prime6809/DragonMMC/DragonFirmware/rsdos/rsdos_mmc.asm

__rsdos
                use     coco-defs.asm
                
dhitok         equ     $e1                      ; highest 1.1 disk token                                     
cyear          equ     '2'                                      


;wd27           equ     $08                     ; uncomment this if using wd2797 on dragon/rs contoler
;wd27            equ     $00                     ; uncomment this if using standard rs-dos or wd2793

;WDRestore       equ     WDCmdRestore+StepRate30ms
;WDSeek          equ     WDCmdSeek+WDFlagVerify+StepRate30ms
;WDStepIn        equ     WDCmdStepIn+WDFlagUpdate+StepRate30ms
;WDStepOut       equ     WDCmdStepOut+WDFlagUpdate+StepRate30ms
;WDReadSector    equ     WDCmdReadSec+wd27       ; read sector command
;WDWriteSector   equ     WDCmdWriteSec+wd27      ; write sector command
;WDWriteTrack    equ     WDCmdWriteTrack

;
;
;
; file allocation table format
;
;
; the file allocation table (fat) contains the status of the granules on a diskette.
; the fat contains 6 control bytes followed by 68 data bytes (one per granule). only the
; first two of the six control bytes are used. a value of $ff is saved in unallocated
; granules. if bits 6 & 7 of the data byte are set, the granule is the last granule
; in a file and bits 0-5 are the number of used sectors in that granule. if bits 6 & 7
; are not set, the data byte contains the number of the next granule in the file.

; offsets to fat control bytes
fat0           equ     0                        ; active file counter : disk to ram fat image disable                                                              
fat1           equ     1                        ; valid data flag: 0=disk data valid, <> 0 = new fat                                                             
;                                         data - disk data invalid
;                2 to 5                   not used
fatcon         equ     6                        ; offset to start of fat data (68 bytes)                                                   
;
;;
;;;; directory entry format
;;
;
; the directory is used to keep track of how many files are stored on a diskette
; and where the file is stored on the disk. the first granule used by the file will
; allow the fat to track down all of the granules used by the file. if the first
; byte of the directory entry is zero, the file has been killed;
; if the first byte is $ff then the directory entry has never been used.
;
;                byte                                description

dirnam         equ     0                        ; file name                      
dirext         equ     8                        ; file extension                           
dirtyp         equ     11                       ; file type                       
dirasc         equ     12                       ; ascii flag                        
dirgrn         equ     13                       ; first granule in file                                   
dirlst         equ     14                       ; number of bytes in last sector                                            
;                16 to 31                            unused
;
;;
;;;; file control block format
;;
;
; the file structure of color trs dos is controlled by a file control block (fcb)
; the fcb contains 25 control bytes and a sector long (256 bytes) data buffer.
; the control bytes control the orderly flow of data from the computer's ram to
; the diskette and vice versa. the open command initializes the fcb; the input,
; output, write, print, get and put commands transfer data through the fcb and
; the close command turns off the fcb.

; tables of offsets to fcb control bytes

;;;;; random file
;                byte                                description
fcbtyp         equ     0                        ; file type: $40=random/direct, 0=closed                                                   
fcbdrv         equ     1                        ; drive number                         
fcbfgr         equ     2                        ; first granule in file                                  
fcbcgr         equ     3                        ; current granule being used                                       
fcbsec         equ     4                        ; current sector being used (1-9)                                            
;                5                                   unused
fcbpos         equ     6                        ; current print position - always zero in random files                                                                 
fcbrec         equ     7                        ; current record number                                  
fcbrln         equ     9                        ; random file record length                                      
fcbbuf         equ     11                       ; pointer to start of this file's random access buffer                                                                  
fcbsof         equ     13                       ; sector offset to current position in record                                                         
fcbflg         equ     15                       ; get/put flag: 0=put, 1=put                                        
;                16,17                               not used
fcbdir         equ     18                       ; directory entry number (0-71)                                           
fcblst         equ     19                       ; number of bytes in last sector of file                                                    

fcbget         equ     21                       ; 'get' record counter: how many characters have been                                                                 
;                                                    pulled out of the current record
fcbput         equ     23                       ; 'put' record counter: pointer to where in the record the next                                                                           
;                                                    byte will be 'put'
;fcbcon         equ     25                          ; offset to start of fcb data buffer (256 bytes)                                                            

;;;;; sequential file (some of these are commented out as they are defined above)
;                byte                                description
;fcbtyp         equ     0                           ; file type: $10=input, $20=output, 0=closed                                                       
;fcbdrv         equ     1                           ; drive number                         
;fcbfgr         equ     2                           ; first granule in file                                  
;fcbcgr         equ     3                           ; current granule being used                                       
;fcbsec         equ     4                           ; current sector being used (1-9)                                            
fcbcpt         equ     5                        ; input file: character pointer - points to next character in                                                                        
;                                                    file to be processed.
;                                                    output file: full sector flag - if it is 1 when the file is
;                                                    closed it means 256 bytes of the last sector have been used.
;fcbpos         equ     6                           ; current print position                                   
;fcbrec         equ     7                           ; current record number: how many whole sectors have been                                                                    
;                                                    input or output to a file.
;                9 to 15                             unused
fcbcfl         equ     16                       ; cache flag: 00=cache empty, $ff=cache full                                                        
fcbcdt         equ     17                       ; cache data byte                             
;fcbdir         equ     18                          ; directory entry number (0-71)                                           
;fcblst         equ     19                          ; number of bytes in last sector of file                                                    
;                 21,22                            unused
fcbdfl         equ     23                       ; input file only: data left flag: 0=data left, $ff=no data (empty)                                                                               
fcblft         equ     24                       ; number of characters left in buffer (input file)                                                              
;                                                  number of chars stored in buffer (output file)
;fcbcon         equ     25                          ; offset to fcb data buffer (256 bytes)                                                   

;               org     $c000                                

;dosbas         fcc     'DK'                                      
;lc002          bra     lc00c                                     

dcnvec         fdb     dskcon                   ; dskcon pointer                                
dskvar         fdb     dcopc                    ; address of dskcon variables                                            
dsinit         fdb     dosini                   ; disk initialization vector                                            
dosvec         fdb     doscom                   ; dos command vector                                    

;
; Init for MMC
;
MMCInit	LBRA	RealMMCInit
;
; Init Dos
; 
DosInit
                ldx     #dbuf0                   ; point x to start of disk ram                                             

lc00f          clr     ,x+                      ; clear a byte                          
               cmpx    #dflbuf                  ; end of disk's ram?                                
               bne     lc00f                    ; no - keep clearing                             

;               ldx     #BeginStub               ; point x to rom image of command interpretation table                                                                
;               ldu     #BasStub2                ; point u to ram address of same                                              
;               ldb     #10                      ; 10 bytes per table                           
;               jsr     UtilCopyBXtoU            ; move (b) bytes from (x) to (u)                                         

;               ldd     #BasSNError              ; syntax error address                                
;               std     $03,u                    ; set jump table addresses of the user command                                                       
;               std     $08,u                    ; interpretation table to point to syntax error                                                        
;               clr     ,u                       ; clear byte 0 of user table (doesn't exist flag)                                                       
;               clr     $05,u                    ; set number of secondary user tokens to zero                                                      

; Modify Extended basic stub
               ldd     #dxcvec                  ; save new                     
               std     BasAddrDskCmdDisp        ; pointers to exbas                                
               ldd     #dxivec                  ; command and secondary                                  
               std     BasAddrDskFuncDisp       ; command interpretation routines                                              

;;;; move the new ram vectors from rom to ram
               ldx     #RamHookTable            ; Point at ram hooks
               ldu     #VectBase                ; point u to 1st ram vector                                     
lc03b          lda     #$7e                     ; op code of jmp instruction                                         
               sta     VectAccessScreen         ; set 1st byte of 'get'/'put' ram vector to 'jmp'                                                           
               sta     ,u+                      ; set 1st byte of ram vector to 'jmp'                                            
               ldd     ,x++                     ; get ram vector from rom                                 
               std     ,u++                     ; store it in ram                         
               cmpx    #DosSignonMess           ; compare to end of rom values                                         
               bne     lc03b                    ; branch if not all vectors moved                                          

               ldx     #DosHookGetPutCLS        ; get rom value of 'get'/'put' ram vector                                                    
               stx     VectAccessScreen+1       ; save it in ram                            
               ldx     #DosHookInterpret        ; get disk command interpretation loop ram vector                                                            
               stx     VectGetNextCmd+1         ; save in ram vector table                                      
    
;;;; initialize disk basic's usr vectors
               ldx     #dusrvc                  ; point x to start of disk basic usr vectors                                                       
               stx     BasUSRTableAddr          ; save start address in BasUSRTableAddr                                        
               ldu     #BasFCError              ; point u to address of 'function call' error                                                       
               ldb     #$0a                     ; 10 user vectors to initialize                                       
lc061          stu     ,x++                     ; set usr vector to 'fc' error                                           
               decb                             ; decrement usr vector counter                                   
               bne     lc061                    ; branch in not done with all 10 vectors                                                 

;               ldx     #dnmisv                  ; get address of nmi servicing routine                                                 
;               stx     SecVecNMI+1              ; save it in nmi vector                                   
;               lda     #$7e                     ; op code of jmp                        
;               sta     SecVecNMI                ; make the nmi vector a jmp                                     
               
;               ldx     #dirqsv                  ; get address of disk basic irq servicing routine                                                            
;               stx     SecVecIRQ+1              ; save it in SecVecIRQ                               
               
               lda     #$13                     ; = initialize write fat                                
               sta     wfatvl                   ; = to disk trigger value                                   
               clr     fatbl0                   ;           
               clr     fatbl1                   ; initialize the active file counter of                                                 
               clr     fatbl2                   ; each fat to zero. this will cause the fats                                                      
               clr     fatbl3                   ; to think there are no active files                                              
               ldx     #dflbuf                  ; = get the starting address of the                                              
               stx     rnbfad                   ; = random file buffer free area and dave it as the                                                             
                                                ; = start address of free ram for random file buffers
               leax    $0100,x                  ; save 256 bytes for random file buffers initially                                                              
               stx     fcbadr                   ; save start address of fcbs                                      
               leax    $01,x                    ; add one and save the starting                                         
               stx     fcbv1                    ; address of fcb1                          
               clr     fcbtyp,x                 ; clear the first byte of fcb 1 (close fcb)                                                       
               leax    fcblen,x                 ; point x to fcb 2                               
               stx     fcbv1+2                  ; save its starting address in fcb vector table                                                          
               clr     fcbtyp,x                 ; clear the first byte of fcb 2 (close fcb)                                                       
               leax    fcblen,x                 ; point x to system fcb - this fcb will only                                                         
                                                ; be used to copy, load, save, merge, etc
               stx     fcbv1+4                  ; save its address in the fcb vector table                                                     
               clr     fcbtyp,x                 ; clear the first byte of system fcb (close fcb)                                                            
               lda     #$02                     ; set the number of active reserved                                           
               sta     fcbact                   ; file buffers to 2 (1,2)                                   
               leax    fcblen,x                 ; point x to one past the end of system fcb                                                        
               tfr     x,d                      ; save the address in accd                                 
               tstb                             ; on an even 256 byte boundary?                                    
               beq     lc0bd                    ; yes              

               inca                             ; no - add 256 to address                              
lc0bd          bita    #$01                     ; check to see if accd is on an even                                                  
               beq     lc0c2                    ; 512 byte (one graphic page) boundary - add                                                     

               inca                             ; 256 (inca) to it if not                              
lc0c2          tfr     a,b                      ; copy acca to accb                               
               addb    #$18                     ; save enough room for 4 graphics pages (pclear 4)                                                           
               stb     BasStartProg             ; save new start of basic address                                           
               jsr     BasLocateScreen          ; initialize exbas variables & do a new                                                

               lda     GrDisplayStartAddr       ; get the start of current graphics page                                                  
               adda    #$06                     ; add 1.5k (6 x 256 = one graphics page)                                                 
               sta     GrLastDisplayAddr        ; save new end of graphics page                                         
               jsr     [dsinit]                 ; initialize swi2,3 jump addresses                                              

;               bsr     InitFDC                  ; go initialize the floppy disk controller                                                   

               andcc   #$af                     ; turn on irq and firq                                
               ldx     #DosSignonMess-1         ; point x to disk basic copyright message                                                     
               jsr     TextOutString            ; print copyright message to screen                                               

;               ldx     #dkwmst                  ; get disk basic warm start address                                              
;               stx     IndVecReset              ; save it in reset vector                                   
;               jmp     la0e2                    ; jump back to basic                             

                jmp	>MMC_InitDone		; do post init stuff


DOSResetVector
               nop                              ; warm start indicator                                
               bsr     InitFDC                  ; initialize the floppy disk controller                                                

               jsr     >CloseFilesInit2         ; close files and do more initialization                                                 
               rts
               
;               jmp     WarmStart                ; jump to exbas' warm start                                     

InitFDC        clr     nmiflg                   ; reset nmi flag                               
               clr     rdytmr                   ; reset drive not ready timer                                       
               clr     drgram                   ; reset ram image of dskreg (motors off)                                                  

;               clr     >dskreg                  ; reset disk control register                                       
;               lda     #WDCmdForceInt           ; force interrupt command of 1793                                         
;               sta     >fdcreg                  ; send it to 1793                           
;               exg     a,a                      ; delay              
;               exg     a,a                      ; delay some more                        
;               lda     >fdcreg                  ; get 1793 status (clear register)                                            
               rts                                     

; disk basic command interp tables
;BeginStub          
;               fcb     NoDOSCommands            ; 20 disk basic 1.1 commands                                       
;               fdb     DosCmdNames              ; disk basic's command dictionary                                          
;               fdb     DosCmdDispatch           ; command jump table                             
;               fcb     NoDOSFunctions           ; 6 disk basic secondary functions                                        
;               fdb     DosFuncNames             ; secondary function table                                   
;               fdb     DosFuncDispatch          ; secondary function jump table                                        

; ram hooks for disk basic
RamHookTable
               fdb     DosHookOpenDev
               fdb     DosHookCheckIONum
               fdb     DosHookRetDevParam                                     
               fdb     DosHookCharOut
               fdb     DosHookCharIn
               fdb     DosHookCheckOpenIn                                
               fdb     DosHookCheckOpenOut
               fdb     DosCloseAllFiles
               fdb     DosHookCloseFile                                
               fdb     CoCoVect179
               fdb     DosHookInput
               fdb     DosHookBreak                                
               fdb     DosHookReadInputLine
               fdb     DosHookTermInputLine
               fdb     DosHookEOF                                
               fdb     DosHookEvaluate
               fdb     DosHookReadInputLine                                
               fdb     DosHookSysError
               fdb     DosHookRun                                

; disk basic copyright message
DosSignonMess  
               fcc     'DISK EXTENDED COLOR BASIC 1.1'                                         
               fcb     cr                                
               fcb      0
               
               ifeq 1
               fcc     'COPYRIGHT (C) 198'                        
               fcb     cyear                                
               fcc     ' BY TANDY'                
               fcb     cr                                
               fcc     'UNDER LICENSE FROM MICROSOFT'                                   
               fcb     cr,cr,0                                
               endc 
               
;disk basic command interpretation handler
DosCmdDispatch cmpa    #dhitok                  ;compare to highest disk basic token                                                     
               bhi     lc244                    ;and branch if higher                              

               ldx     #CommandDispatchTable    ; point x to disk basic command jump table                                                    
               suba    #$ce                     ; subtract out lowest disk basic command token                                                       
               jmp     BasDoDispatch            ; jump to basic's command handler                                          


lc244          cmpa    #dhitok                  ; compare to highest disk basic token                                                      
               lbls    BasSNError               ; 'syntax' error if < disk basic command token                                                        

               jmp     [BasStub3+3]             ; process a user command token                                             


;disk basic secondary command interpretation handler
DosFuncDispatch
               cmpb    #($a7-$80)*2             ;compare modified secondary token to                                                                                    
               bls     lc256                    ;highest disk basic token & branch if higher                                                     

               jmp     [BasStub3+8]             ; jump to user secondary command handler                                                        


lc256          subb    #($a2-$80)*2             ;subtract out the smallest secondary                                                                                    
               pshs    b                        ;disk token & save modified token on the stack                                                    
               jsr     lb262                    ; syntax check for '(' and evaluate expression                                                       


               puls    b                        ; restore modified token                              
               ldx     #FunctionDipatchTable                   ; point x to secondary command jump table                                                   
               jmp     lb2ce                    ; jump to basic's secondary command handler                                                    


; error driver ram vector
DosHookSysError
	       puls    y                        ; put the return address into y                                           
               jsr     BasResetStack            ; reset the cont flag, etc                                   

               jsr     >CloseFilesInit2                   ; initialize some disk variables and close files                                                         


               pshs    y,b                      ; put return address and error number on the stack                                                          
               jsr     >DosCloseAllFiles                   ; close all files                          

               puls    b                        ; get the error number back                                 

               cmpb    #2*27                    ; compare to the lowest disk error number                                                                                  
               lbcs    CoCoVect191              ; branch to exbas error handler if not disk error number                                                                   

               leas    $02,s                    ; purge return address off the stack                                              
               jsr     la7e9                    ; turn off the cassette motor                                      

               jsr     SndDisable               ; disable the analog multiplexer                                         


               clr     TextDevN                 ; set device number to the screen                                           
               jsr     lb95c                    ; send a cr to the screen                                  

               jsr     TextOutQuestion          ; send a '?' to the screen                                   

               ldx     #DosErrorCodeTable-(2*27)            ; point x to disk basic's error table                                                                           
               jmp     SysErr2                  ; jump to basic's error handler                                        


; disk basic error messages
DosErrorCodeTable          
                fcc     'BR'                    ; 27 bad record                            
                fcc     'DF'                    ; 28 disk full                      
                fcc     'OB'                    ; 29 out of buffer space                                
                fcc     'WP'                    ; 30 write protected                            
                fcc     'FN'                    ; 31 bad file name                          
                fcc     'FS'                    ; 32 bad file structure                               
                fcc     'AE'                    ; 33 file already exists                                
                fcc     'FO'                    ; 34 field overflow                           
                fcc     'SE'                    ; 35 set to non-fielded string                                      
                fcc     'VF'                    ; 36 verification error                               
                fcc     'ER'                    ; 37 write or input past end of record                                              
                        
; disk file extensions
basext          fcc     'BAS'                   ; basic file extension                                     
defext          fcc     '   '                   ; ' blank (default) file extension                                             
datext          fcc     'DAT'                   ; data file extension                                    
binext          fcc     'BIN'                   ; binary file extension                                      
                        
; cls ram vector
DosHookGetPutCLS         pshs    x,cc                     ; save x reg and status                                      
               ldx     $03,s                    ; load x with calling address                                      
               cmpx    #l975f                   ; coming from exbas' get/put?                                        
               bne     lc2bf                    ; no             

               cmpa    #'#                      ; number sign (get#, put#)?                                    
               beq     lc2c1                    ; branch if get or put to random file                                              

lc2bf          puls    cc,x,pc                  ; restore x reg, status and return                                                   

; get/put to a direct/random file
lc2c1          leas    $05,s                    ; purge return address and registers off of the stack                                                                    
               jsr     >lc82e                   ; evaluate device number & set fcb pointer                                                   

               stx     fcbtmp                   ; save fcb pointer                            
               clr     fcbget,x                 ; reset the get                           
               clr     fcbget+1,x               ; data pointer                            
               clr     fcbput,x                 ; = reset the put                             
               clr     fcbput+1,x               ; = data pointer                              
               clr     fcbpos,x                 ; reset print position counter                                          
               lda     fcbdrv,x                 ;get the fcb drive number and                                         
               sta     dcdrv                    ;save it in dskcon variable                                    
               jsr     BasChrGetCurr            ; get current input character from basic                                                  

               beq     lc2ea                    ; branch if end of line                                

               jsr     VarCKComma               ; syntax check for comma                                    

               jsr     VarGet16Bit              ; evaluate expression - return in (x)                                              

               tfr     x,d                      ; save record number in accd                                   
lc2e6          ldx     fcbtmp                   ; point x to fcb                               
               std     fcbrec,x                 ; save record number in fcb                                       
lc2ea          ldd     fcbrec,x                 ; get record number                                    
               beq     lc30b                    ; 'bad record' error if record number = 0                                                  

               jsr     >lc685                   ; increment record number                                  

               ldd     fcbrln,x                 ; get random file record length and random file                                                           
               ldx     fcbbuf,x                 ; buffer pointer and save them on the stack -                                                         
               pshs    x,b,a                    ; these are the initial values of a temporary                                                       
                                                ; record length counter and random buffer
                                                ; pointer which are maintained on the stack
               leax    $-2,u                    ; point x to (record number -1)                                         
               jsr     l9fb5                    ; mult (unsigned) record length x (record number -1)                                                             

               pshs    u,y                      ; save product on the stack                                   
               lda     ,s+                      ; check ms byte of product                                 
               bne     lc30b                    ; 'br' error if not zero (record number too big)                                                         

               puls    x                        ; pull the bottom 3 product bytes off the stack;                                                      
               puls    b                        ; top two in x, bottom in accb; accb points to                                                    
                                                ; the first byte of the sector used by this record,
                                                ; (x) contains the sector offset (in which sector
                                                ; from the start the byte is located)
lc306          cmpx    #(trkmax-1)*secmax       ; 612 sectors max in a random file                                                       
               blo     lc310                    ; branch if record length o.k.                                       

lc30b          ldb     #2*27                    ; 'bad record' error                                                            
               jmp     SysErr                   ; jump to error handler                                

lc310          ldu     fcbtmp                   ; point u to fcb                               
               cmpx    fcbsof,u                 ; compare saved sector offset to the current sector offset                                                                       
               lbeq    lc3cf                    ; being processed - do not process a new sector if they are equal                                                                           

               pshs    x,b                      ; save byte and sector offset to record start on stack                                                              
               lda     fcbflg,u                 ; check fcb get/put flag and                                        
               beq     lc324                    ; branch if it was a get                                 

               clr     fcbflg,u                 ; force get/put to 'put'                                    
               ldb     #$03                     ; dskcon write op code                              
               bsr     lc357                    ; go write a sector - save 'put' data on disk                                                      


;; convert the sector offset to a granule and sector number
lc324          ldd     $01,s                    ; get the number of sectors to the start of                                                         
               jsr     >lc784                   ; this record number and convert them to a granule offset                                                                  

               pshs    b                        ; save granule offset on the stack                                        
               jsr     >lc779                   ; multiply granule number x 9 - convert to number of sectors                                                                     

               negb                             ; negate ls byte of granule offset and add the                                                   
               addb    $03,s                    ; ls byte of sector offset - accb = sector                                                    
                                                ; number (0-8) corresponding to the sector number within a
                                                ; granule of the last sector of the sector offset
               incb                             ; = add one - sectors saved in the fcb; start                                                  
               stb     fcbsec,u                 ; = at 1 not 0 - save it in the fcb                                               
               ldb     fcbfgr,u                 ; get first granule in file                                       
               jsr     >lc755                   ; point x to fat                         

               leau    fatcon,x                 ; point u to fat data                                  
               lda     ,s                       ; get number of granules offset to record                                               
               inca                             ; add one (compensate for deca below)                                          
lc33e          leax    ,u                       ; point x to fat data                                 
               abx                              ; point x to correct granule                                
               deca                             ; decrement granule counter                                
               beq     lc37b                    ; branch if correct granule found                                          

               stb     ,s                       ; save granule address on stack                                     
               ldb     ,x                       ; get next granule in file                                
               cmpb    #$c0                     ; last granule in file?                                
               blo     lc33e                    ; no - keep looking                            


; the granule being searched for is not presently defined in this random file
               ldb     ,s                       ; get offset to last granule                                  
               tst     vd8                      ; check get/put flag                           
               bne     lc366                    ; and branch if put                            

lc352          ldb     #2*23                    ;'input past end of file' error                                                                        
               jmp     SysErr                   ; jump to error handler                                

lc357          leax    fcbcon,u                 ; point x to fcb data buffer                                              

; read/write a sector. enter with op code in accb, buffer ptr in x
lc35a          stb     dcopc                    ; save dskcon operation code variable                                                   
               stx     dcbpt                    ; save dskcon load buffer variable                                           
               leax    ,u                       ; point x to fcb                       
               jsr     >lc763                   ; convert fcb track and sector to dskcon variables                                                           

               jmp     >DoDiskReadWrite                   ; read/write a track or sector                                       


; 'put' data into a granule not presently included in this file
lc366          pshs    x,a                      ; save granule counter and pointer to last used granule                                                                    
               jsr     >lc7bf                   ; find first free granule in fat                                         

               tfr     a,b                      ; save free granule number in accb                                         
               puls    a,u                      ; pull last granule pointer and counter off of stack                                                            
               stb     ,u                       ; save newly found granule number in address of last granule                                                                  
               deca                             ; decrement granule counter                                
               bne     lc366                    ; get another granule if not done                                          

               pshs    x,b                      ; save pointer to last granule and offset                                                 
               jsr     >lc71e                   ; write fat to disk                            

               puls    b,x                      ; restore pointer and offset                                    

; when correct granule is found, find the right sector
lc37b          leas    $01,s                    ; remove gran number from stack                                              
               ldu     fcbtmp                   ; point u to fcb                          
               stb     fcbcgr,u                 ; save current granule in fcb                                         
               lda     #$ff                     ;set fcbsof,u to illegal sector offset which will                                                         
               sta     fcbsof,u                 ;force new sector data to be read in                                                
               lda     ,x                       ; get current granule                           
               cmpa    #$c0                     ; is it the last granule?                                  
               blo     lc3b2                    ; no             

               anda    #$3f                     ; mask off last granule flag bits                                          
               cmpa    fcbsec,u                 ; compare calculated sector to current sector in fcb                                                                 
               bhs     lc3b2                    ; and branch if calculated sector is > last sector in file                                                                   

               lda     vd8                      ; = check get/put flag: if 'get' then 'input                                                   
               beq     lc352                    ; = past end of file' error                                    

               lda     fcbsec,u                 ; get current sector number from fcb,                                                 
               ora     #$c0                     ; or in the last granule flag bits                                          
               sta     ,x                       ; and save in fat                       
               jsr     >lc5a9                   ; write fat to disk if necessary                                         

               ldx     fcbrln,u                 ; get record length and check to                                            
               cmpx    #seclen                  ; see if it is seclen (exactly one sector)                                                      
               bne     lc3ad                    ; branch if it is not exactly one sector                                                 

               cmpx    fcblst,u                 ; =branch if the number of bytes in the last sector                                                                

               beq     lc3b2                    ; =is set to one sector (seclen)                                         

               lda     #$81                     ;set the presaved flag (bit15) and force                                                
lc3ac          fcb      Skip1                    ;brn
lc3ad          clra                             ; set the number of bytes in last sector to zero                                                          
               clrb                             ; clear ls byte of accd                            
               std     fcblst,u                 ; save the number of bytes in last sector                                                     

lc3b2          ldb     #$02                     ; dskcon read op code                                  
               ldx     fcbrln,u                 ; get record length and compare                                           
               cmpx    #seclen                  ; it to seclen - exactly one sector                                               
               bne     lc3c8                    ; branch if not exactly one sector long                                                

               leas    $07,s                    ; clean up stack                          
               ldx     fcbbuf,u                 ; point x to start of random file buffer                                                    
               lda     vd8                      ; check get/put flag and                               
               beq     lc3c5                    ; branch if get                        

               ldb     #$03                     ; dskcon write op code                              
lc3c5          jmp     >lc35a                   ; read/write a sector                                   

lc3c8          jsr     >lc357                   ; read a sector into fcb data buffer                                                  

               puls    b,x                      ; get back the byte offset to record: x = number of                                                           
                                                ; sectors; accb = byte pointer in sector
               stx     fcbsof,u                 ; save sector offset in fcb                                       
lc3cf          pshs    b                        ; save byte offset on stack                                      
               jsr     >lc755                   ; point x to file allocation table                                           

               leax    fatcon,x                 ; move x to fat data                                 
               ldb     fcbcgr,u                 ; get current granule number                                        
               abx                              ; point x to proper granule in fat                                      
               lda     ,x                       ; get current granule and check to                                        
               cmpa    #$c0                     ; see if it is last granule                                    
               blo     lc40a                    ; branch if this granule is < last granule                                                   

               anda    #$3f                     ; mask off last granule flag bits                                          
               cmpa    fcbsec,u                 ; compare last sector used in granule to                                                     
               bne     lc40a                    ; calculated sector; branch if not equal                                                 

               ldd     fcblst,u                 ; get number of bytes in last sector                                                

               anda    #$7f                     ; mask off presaved flag (bit 15)                                          
               pshs    b,a                      ; save number of bytes in last sector on stack                                                      
               clra                             ; load accb with the byte offset to current                                                
               ldb     $02,s                    ; record and add the remaining record length                                                     
               addd    $03,s                    ; to it - accd = end of record offset                                               
               cmpd    ,s++                     ; =compare the end of record offset to the number of                                                             
               bls     lc40a                    ; =bytes used in the last sector                                         

               tst     vd8                      ; check get/put flag and branch if 'get'                                               
               lbeq    lc352                    ; to 'input past end of file' error                                             


; if last used sector, calculate how many bytes are used
; if data is being 'put' pasth the current end of file
               cmpd    #seclen                  ; compare to one sector's length                                            
               bls     lc405                    ; branch if remainder of record length will fit in this sector                                                                       

               ldd     #seclen                  ; force number of bytes = one sector length                                                      
lc405          ora     #$80                     ; set pre-saved flag bit - all put records are                                                           
                                                ; written to disk before leaving 'put'
               std     fcblst,u                 ; save number of bytes used in last sector                                                      

lc40a          puls    b                        ; pull byte offset off of the stack                                              
               leax    fcbcon,u                 ; point x to fcb data buffer                                         
               abx                              ; move x to start of record                               
               ldu     $02,s                    ; point u to current position in random file buffer                                                            
               pshs    b                        ; save byte offset on stack                                 
               lda     #-1                      ; convert accd into a negative 2 byte number                                                   
                                                ; representing the remaining unused bytes in the sector
               addd    $01,s                    ; add temporary record length counter (subtract                                                         
                                                ; remaining bytes from temporary record length)
               bhs     lc421                    ; branch if there are enough unused bytes to finish the record                                                                       

               std     $01,s                    ; save new temporary record length counter                                                   
               puls    b                        ; restore byte counter                            
               negb                             ; negate it - accb = the number of bytes                                             
                                                ; available to a record in this sector
               bra     lc429                    ; move the data                        

; branch here if remaining record length will fit in
; what's left of the currently selected sector
lc421          ldb     $02,s                    ; get remaining record length                                           
               clr     $01,s                    ; clear the temporary record length                                            
               clr     $02,s                    ; counter on the stack                               
               leas    $01,s                    ; purge byte offset from stack                                        
lc429          lda     vd8                      ; check get/put flag and                                    
               beq     lc42f                    ; branch if get                        

               exg     x,u                      ; swap source and destination pointers                                             
lc42f          jsr     UtilCopyBXtoU            ; transfer data from source to destination buffers                                                                

               stu     $02,s                    ; save new temp record pointer on the stack (get)                                                          

; move data from fcb data buffer to the random file buffer if 'get'
; or from random file buffer to fcb data buffer if 'put'
               ldu     fcbtmp                   ; point u to fcb                          
               lda     vd8                      ; check get/put flag and                               
               beq     lc43e                    ; branch if get                        

               sta     fcbflg,u                 ; save 'put' flag in the fcb                                        
               stx     $02,s                    ; save new temporary record pointer on stack (put)                                                           
lc43e          ldx     fcbsof,u                 ; get sector offset counter and                                                
               leax    $01,x                    ; add one to it                         
               clrb                             ; set byte offset = 0                          
               ldu     ,s                       ; check the length of the temporary record length                                                       
               lbne    lc306                    ; counter and keep moving data if <> 0                                                

               puls    a,b,x,pc                 ; pull temporary record length and                                               
                                                ; buffer address off stack and return

; open ram hook
DosHookOpenDev 
               leas    $02,s                    ; pull return address off of the stack                                                     
               jsr     VarGetStr                ; evaluate an expression                                 

               jsr     BasGetStrFirst           ;get mode(i,o,r) - first byte of string expression                                                           

               pshs    b                        ;and save it on stack                           
               jsr     BasGetDevNo              ; get device number                            

               tstb                             ; set flags                
               lble    CmdOpenEntry             ; branch if not a disk file                                     
               puls    a                        ; get mode                
               pshs    b,a                      ; save mode and device number (file number)                                                   
               clr     TextDevN                 ; set device number to screen                                       
               jsr     VarCKComma               ; syntax check for comma                                    

               ldx     #datext                  ; point to 'dat' for extension                                         
               jsr     >lc938                   ; get filename from basic                                  

               ldd     #$01ff                   ; default disk file type and ascii flag                                                 
               std     dfltyp                   ; save default values: data, ascii                                            
               ldx     #seclen                  ; default record length - 1 page                                           
               jsr     BasChrGetCurr            ; get char from basic                               

               beq     lc481                    ; branch if end of line                                

               jsr     VarCKComma               ; syntax check for comma                                    

               jsr     lb3e6                    ; evaluate expression                              

               ldx     BasVarFPAcc1+3           ; get evaluated expression                                    
lc481          stx     dfflen                   ; record length                              
               lbeq    BasFCError               ; if = 0, then 'illegal function call'                                                

               jsr     la5c7                    ; error if any further characters on line                                                  

               puls    a,b                      ; get mode and file number                                  

; open disk file for read or write
lc48d          pshs    a                        ; save mode on stack                               
               jsr     >lc749                   ; point x to fcb for this file                                       

               lbne    la61c                    ; 'file already open' error if file open                                                  

               stx     fcbtmp                   ; save file buffer pointer                                    
               jsr     >GetFAT                   ; make sure file alloc table is valid                                              

               jsr     >lc68c                   ; scan directory for 'filename.ext'                                            

               puls    b                        ; get mode                
               lda     #inpfil                  ; input type file                            
               pshs    a                        ; save file type on stack                               
               cmpb    #'I                      ; input mode?                      
               bne     lc4c7                    ; branch if not                        


; open a sequential file for input
               jsr     >lc6e5                   ; check to see if directory match is found                                                   

               jsr     >lc807                   ; check to see if file already open                                            

               ldx     v974                     ; get ram directory buffer                                  
               ldd     dirtyp,x                 ; get file type and ascii flag                                          
               std     dfltyp                   ; save in ram image                             
               bsr      lc52d

               jsr     >lc627                   ; go fill data buffer                              

lc4bb          jsr     >lc755                   ; point x to proper file allocation table                                                       

               inc     fat0,x                   ; add one to fat active file counter                                              
               ldx     fcbtmp                   ; get file buffer pointer                                   
               puls    a                        ; get file type                     
               sta     fcbtyp,x                 ; save it in fcb                            
               rts                                     

lc4c7          asl     ,s                       ; set file type to output                                    
               cmpb    #'O                      ; file mode = output?                              
               bne     lc4e8                    ; branch if not                        


; open a sequential file for output
               tst     v973                     ; does file exist on directory?                                       
               beq     lc4e1                    ; branch if not                        

               jsr     >lc6cf                   ; kill the old file                            

               lda     v973                     ; get directory sector number of old file and                                                     
               sta     v977                     ; save it as first free directory entry                                               
               ldx     v974                     ; =get ram directory image of old file and                                                  
               stx     v978                     ; =save it as first free directory entry                                                

lc4e1          jsr     >lc567                   ; set up new directory entry on disk                                                  

               bsr     lc538                    ; initialize file buffer                                 

               bra     lc4bb                    ; flag and map fcb as being used                                         
lc4e8          cmpb    #'R                      ; file mode = r (random)?                                       
               beq     lc4f2                    ; branch if so                       

               cmpb    #'D                      ; file mode = d (direct)?                                  
               lbne    BasFMError               ; 'bad file mode' error if not                                        


; open a random/direct file
lc4f2          asl     ,s                       ; set file type to direct                                    
               ldd     rnbfad                   ; get address of random file buffer area                                                  
               pshs    b,a                      ; and save it on the stack                                  
               addd    dfflen                   ; add the record length                                  
               blo     lc504                    ; 'ob' error if sum > $ffff                                    

               cmpd    fcbadr                   ; is it > than fcb data area?                                        
               bls     lc509                    ; branch if not                        

lc504          ldb     #2*29                    ;'out of buffer space' error                                                                         
               jmp     SysErr                   ; jump to error handler                                

lc509          pshs    b,a                      ; save end of random buffer on stack                                                 
               tst     v973                     ; did this file exist                             
               bne     lc514                    ; branch if so                       

               bsr     lc567                    ; set up new file in directory                                       

               bra     lc519                    ; initialize fcb                         
lc514          lda     #$ff                     ; set file type match = $ff (illegal value) -                                                          
               jsr     >lc807                   ; this will force any open matched file to cause                                                         

                                                ; a 'file already open' error
lc519          bsr     lc52d                    ; initialize fcb                              

               com     fcbsof,x                 ; set fcbsof,x to $ff (illegal sector offset) which will                                                                    
                                                ; force new sector data to be read in during get/put
               inc     fcbrec+1,x               ; initialize record number = 1                                            
               puls    a,b,u                    ; u = start of random file buffer area, accd = end                                                            
               std     rnbfad                   ; save new start of random file buffer area                                                     
               stu     fcbbuf,x                 ; save buffer start in fcb                                      
               ldu     dfflen                   ; get random file record length                                         
               stu     fcbrln,x                 ; and save it in fcb                                
               bra     lc4bb                    ; set fat flag, save file type in fcb                                              

; initialize fcb data for input
lc52d          bsr     lc538                    ; initialize fcb                              

               ldu     v974                     ; get ram directory image                                 
               ldu     dirlst,u                 ;get number of bytes in last sector of file                                                        
               stu     fcblst,x                 ;save it in fcb                           

               rts                                     

; initialize file control block
lc538          ldx     fcbtmp                   ; get current file buffer                                        
               ldb     #fcbcon                  ; clear fcb control bytes                                    
lc53c          clr     ,x+                      ; clear a byte                          
               decb                             ; decrement counter                        
               bne     lc53c                    ; branch if not done                             

               ldx     fcbtmp                   ; get current file buffer address back                                                
               lda     dcdrv                    ;get current drive number and                                      
               sta     fcbdrv,x                 ;save it in fcb                           
               lda     v976                     ; =get first granule -                              
               sta     fcbfgr,x                 ; =save it as the starting granule number and                                                         
               sta     fcbcgr,x                 ; =save it as current granule number                                                
               ldb     v973                     ; get directory sector number                                     
               subb    #$03                     ; subtract 3 - directory sectors start at 3                                                    
               aslb                             ; multiply sectors                       
               aslb                             ; by 8 (8 directory                        
               aslb                             ; entries per sector)                          
               pshs    b                        ; save sector offset                          
               ldd     v974                     ; get ram directory image                                 
               subd    #dbuf0                   ; subtract ram offset                                
               lda     #$08                     ; 8 directory entries/sector                                    
               mul                              ; now acca contains 0-7                           
               adda    ,s+                      ; acca contains directory entry (0-71)                                              
               sta     fcbdir,x                 ; save directory entry number                                         
               rts                                     


; set up directory and update file allocation table entry in first unused sector
lc567          ldb     #28*2                    ;'disk full' error                                                               
               lda     v977                     ; get sector number of first empty directory entry                                                          
               lbeq    SysErr                   ; 'disk full' error if no empty directory entries                                                           

               sta     v973                     ; save sector number of first empty directory entry                                                           
               sta     dsec                     ; save sector number in dskcon register                                               
               ldb     #$02                     ; read op code                      
               stb     dcopc                    ; save in dskcon register                                  
               jsr     >DoDiskReadWrite                   ; read sector                      

               ldx     v978                     ; get address of ram image of unused directory                                                      
               stx     v974                     ; entry and save as current used ram image                                                  
               leau    ,x                       ; (tfr x,u) point u to directory ram image                                                 
               ldb     #dirlen                  ; set counter to clear 32 bytes (directory entry)                                                            
lc586          clr     ,x+                      ; clear byte                        
               decb                             ; decrement counter                        
               bne     lc586                    ; continue if not done                               

               ldx     #dnambf                  ; point to filename and extension ram image                                                      
               ldb     #11                      ; 11 bytes in filename and extension                                           
               jsr     UtilCopyBXtoU            ; move b bytes from x to u                                   

               ldd     dfltyp                   ; get file type and ascii flag                                        
               std     $00,u                    ; save in ram image                            
               ldb     #33                      ; first granule to check                               
               jsr     >lc7bf                   ; find the first free granule                                      

               sta     v976                     ; save in ram                     
               sta     $02,u                    ; save in ram image of directory track                                               
               ldb     #$03                     ; get write operation code and save                                           
               stb     dcopc                    ; it in dskcon register                                
               jsr     >DoDiskReadWrite                   ; go write a sector in directory                                         

lc5a9          pshs    u,x,b,a                  ; save registers                                 
               jsr     >lc755                   ; point x to file allocation table                                           

               inc     fat1,x                   ; indicate new data in file alloc table                                                 
               lda     fat1,x                   ; get new data flag                             
               cmpa    wfatvl                   ; have enough granules been removed from the fat to                                                              
                                                ; cause the fat to be written to the disk
               blo     lc5ba                    ; return if no need to write out allocation table                                                          

               jsr     >lc71e                   ; write file allocation sector to disk                                               

lc5ba          puls    a,b,x,u,pc               ; restore registers
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
